makerspace-wi/Project-CNC-3/doc/MMS/MMS_Schematik.pdf

# Schematische Darstellung der ColdEND MMS

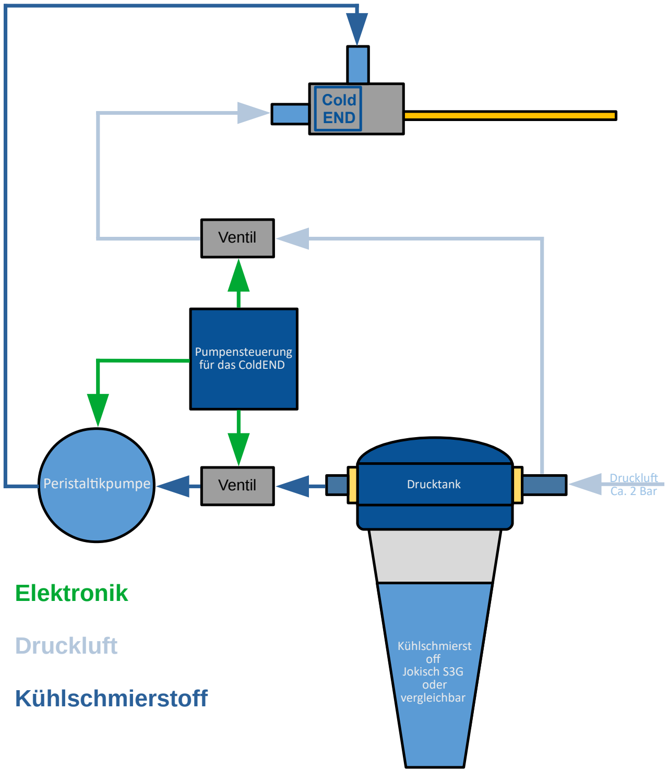
[picture p23: figure]
Peristaltikpumpe; Pumpensteuerung für das ColdEND; Drucktank; Kühlschmierst off Jokisch S3G oder vergleichbar; Druckluft Ca. 2 Bar; Cold END; Elektronik; Druckluft; Kühlschmierstoff; Ventil

© Sebastian End - End-CNC
