makerspace-wi/Project-CNC-3/docs/images/IMG_5434 2.jpg

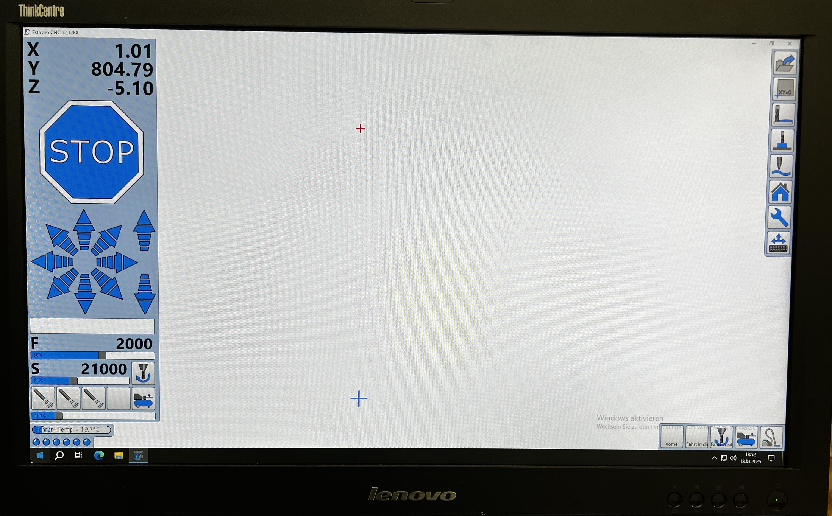
docs/images/IMG_5434 2.jpg
