makerspace-wi/Project-CNC-3/docs/images/Screenshot 2026-01-06 182346.png

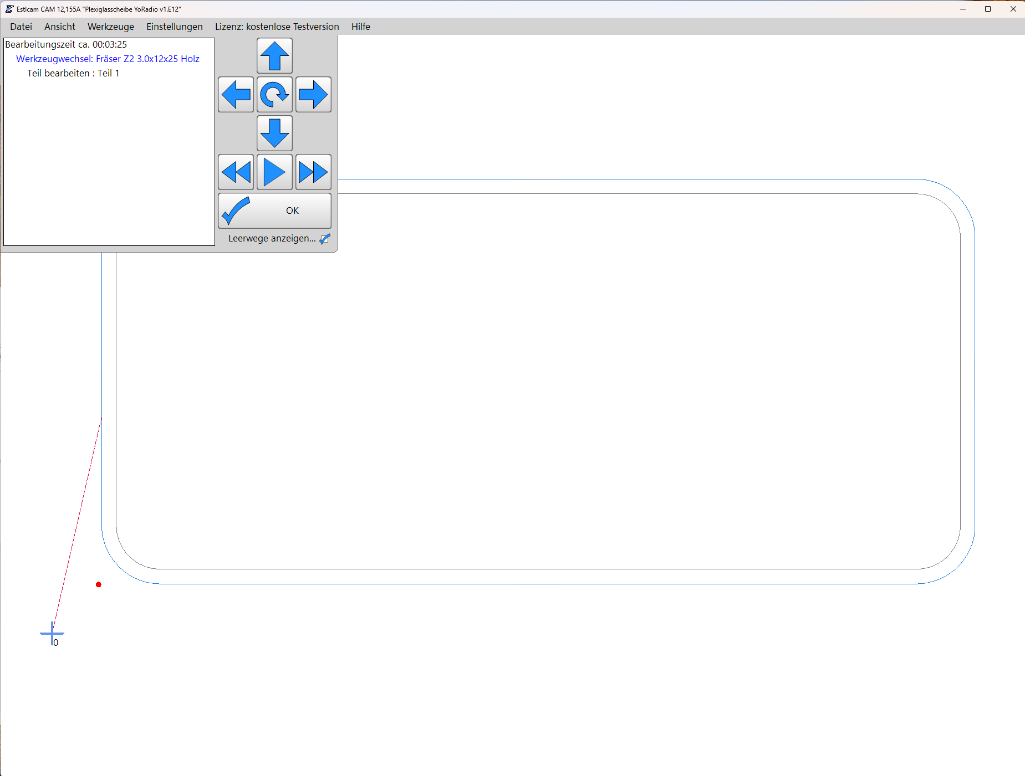
docs/images/Screenshot 2026-01-06 182346.png
