makerspace-wi/Project-CNC-3/docs/images/screenshot_04.PNG

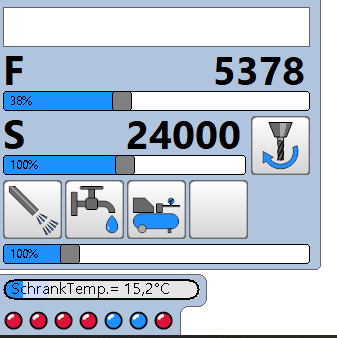
docs/images/screenshot_04.PNG
