makerspace-wi/Project-CNC-3/docs/images/Zwischenablage-2.png

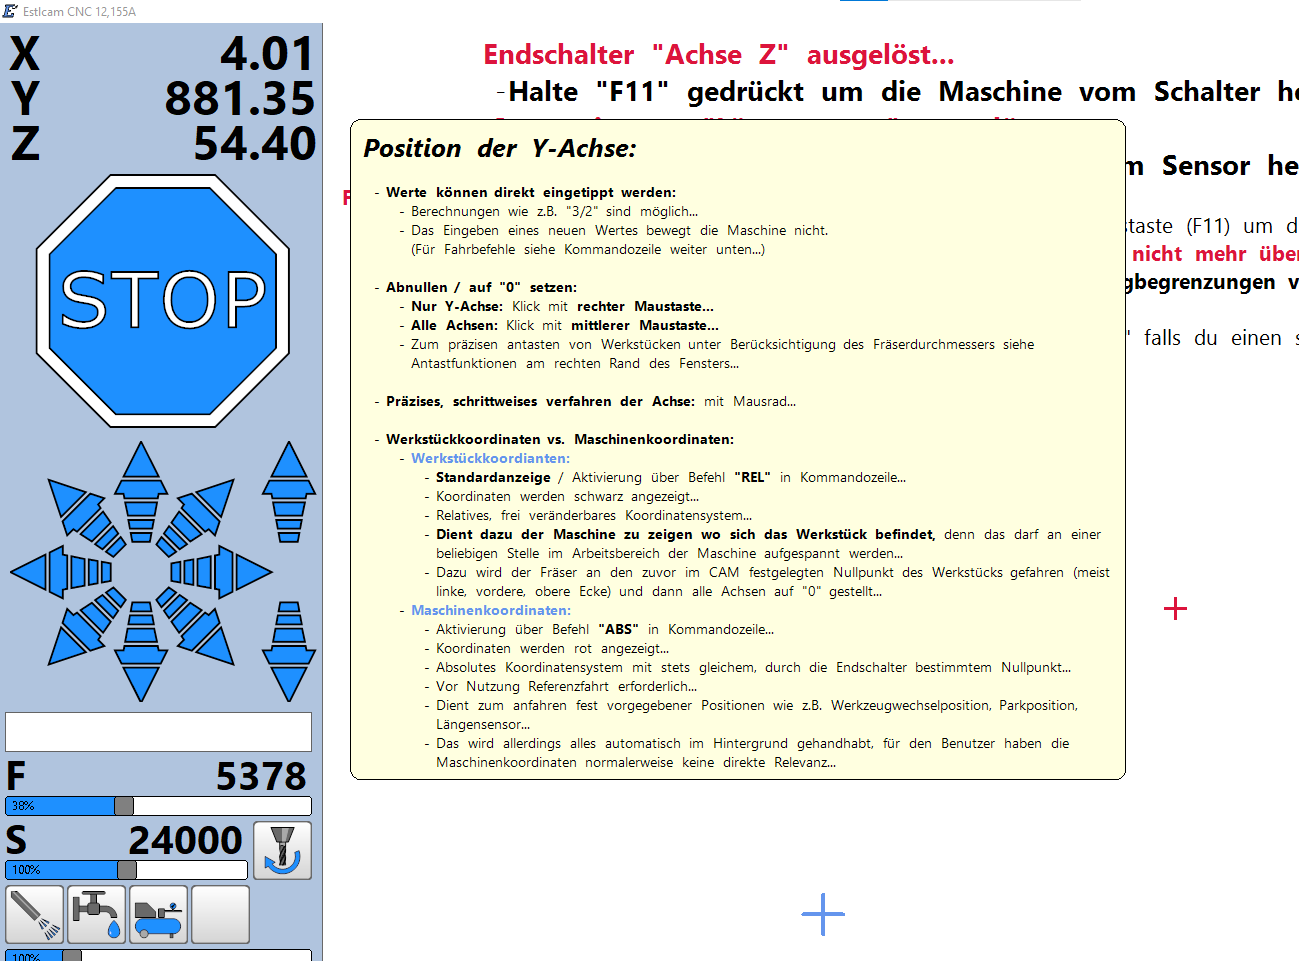
docs/images/Zwischenablage-2.png
